solarmon/RGBtoHDMI-CDTV-v2/RGBtoHDMI CDTV v2/RGBtoHDMI CDTV v2 - Daughter Board - Top.png

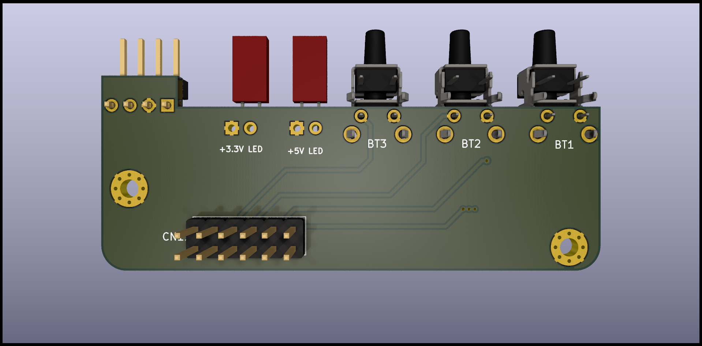
RGBtoHDMI CDTV v2/RGBtoHDMI CDTV v2 - Daughter Board - Top.png
