solarmon/RGBtoHDMI-CDTV-v2/RGBtoHDMI CDTV v2/gerbers/video-slot/RGBtoHDMI CDTV v2-Edge_Cuts.dxf

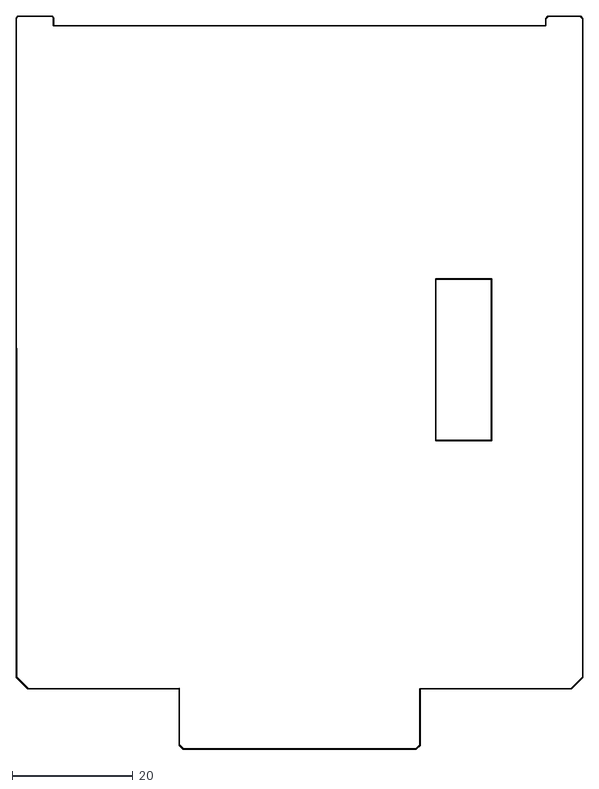
[picture p29: CAD file, 2022-10-09]
RGBtoHDMI CDTV v2/gerbers/video-slot/RGBtoHDMI CDTV v2-Edge_Cuts.dxf
94.0 x 121.6
