solarmon/RGBtoHDMI-CDTV-v2/RGBtoHDMI CDTV v2/RGBtoHDMI CDTV v2 - Face Plate.step

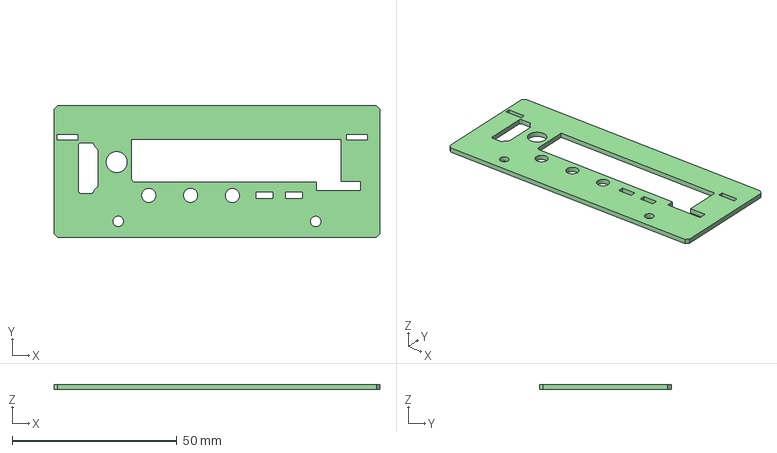
[picture p30: CAD file, 2022-10-09]
RGBtoHDMI CDTV v2/RGBtoHDMI CDTV v2 - Face Plate.step
99.0 x 40.0 x 1.60 mm
