solarmon/RGBtoHDMI-CDTV-v2/RGBtoHDMI CDTV v2 - Denise Breakout/gerber/RGBtoHDMI CDTV v2 - Denise Breakout-F_Cu.dxf

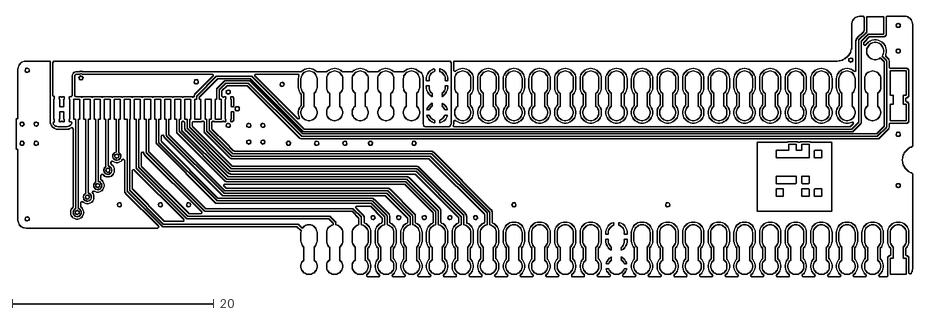
[picture p31: CAD file, 2022-10-09]
RGBtoHDMI CDTV v2 - Denise Breakout/gerber/RGBtoHDMI CDTV v2 - Denise Breakout-F_Cu.dxf
88.9 x 25.8
