solarmon/RGBtoHDMI-CDTV-v2/RGBtoHDMI CDTV v2 - Mouse and Joystick Adapter/gerber/ffc-extender/RGBtoHDMI CDTV v2 - Mouse and Joystick Adapter - FFC Extender-B_Cu.dxf

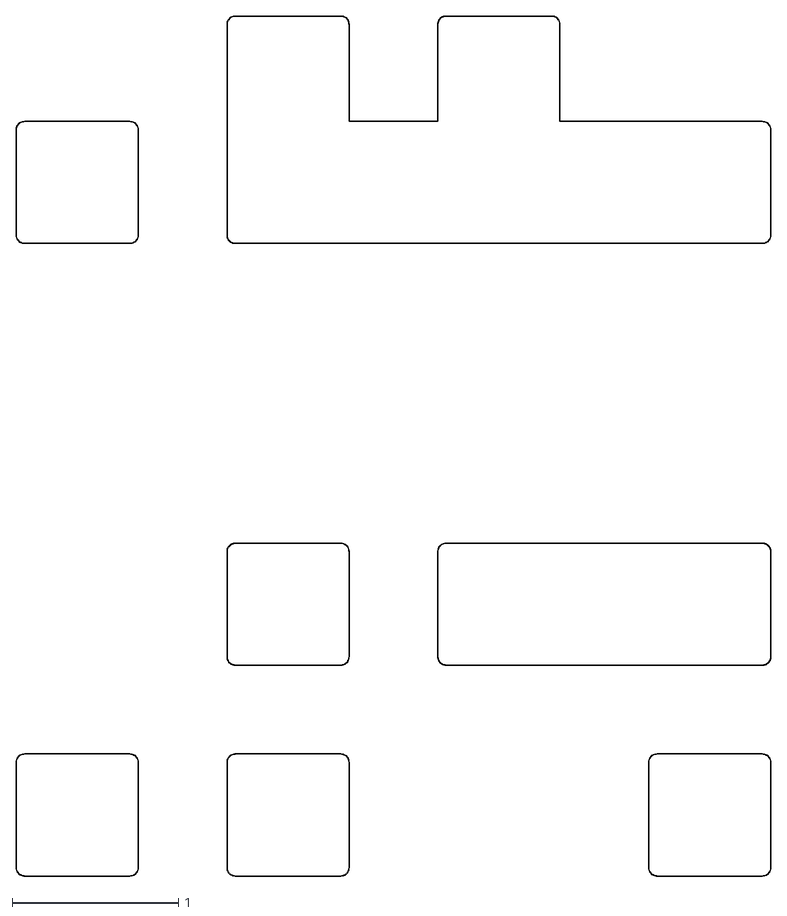
[picture p32: CAD file, 2022-10-09]
RGBtoHDMI CDTV v2 - Mouse and Joystick Adapter/gerber/ffc-extender/RGBtoHDMI CDTV v2 - Mouse and Joystick Adapter - FFC Extender-B_Cu.dxf
4.55 x 5.18
