solarmon/RGBtoHDMI-CDTV-v2/RGBtoHDMI CDTV v2 - Mouse and Joystick Adapter/gerber/mouse-joystick-adapter/RGBtoHDMI CDTV v2 - Mouse and Joystick Adapter-F_Cu.dxf

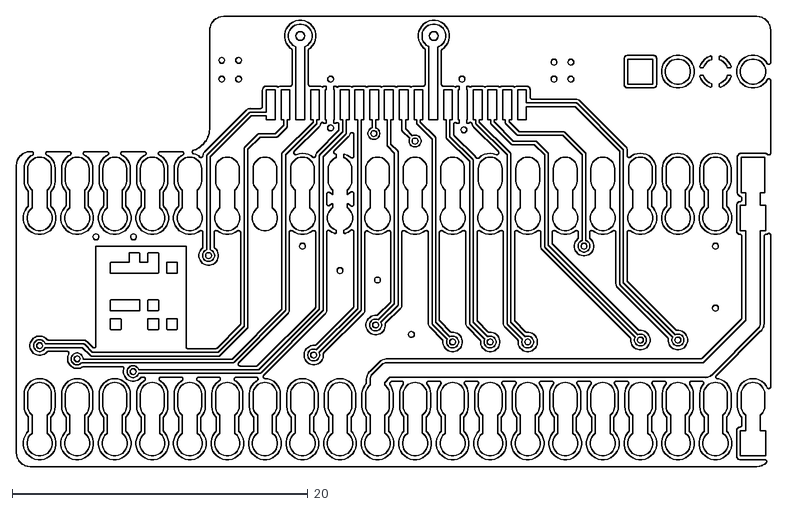
[picture p33: CAD file, 2022-10-09]
RGBtoHDMI CDTV v2 - Mouse and Joystick Adapter/gerber/mouse-joystick-adapter/RGBtoHDMI CDTV v2 - Mouse and Joystick Adapter-F_Cu.dxf
51.0 x 30.5
