solarmon/RGBtoHDMI-CDTV-v2/RGBtoHDMI CDTV v2/gerbers/daughter-board/RGBtoHDMI CDTV v2 - Daughter Board-B_Cu.dxf

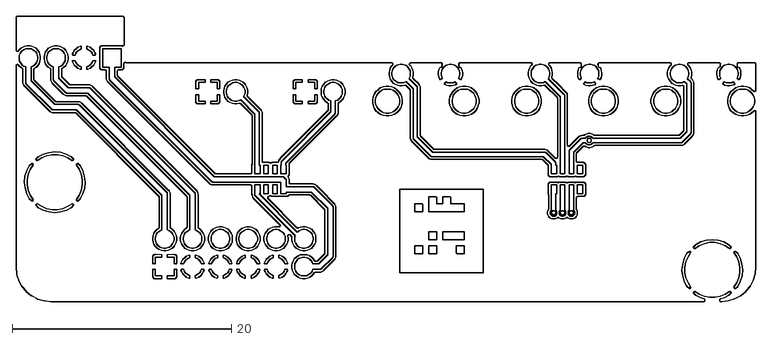
[picture p34: CAD file, 2022-10-09]
RGBtoHDMI CDTV v2/gerbers/daughter-board/RGBtoHDMI CDTV v2 - Daughter Board-B_Cu.dxf
67.5 x 26.0
