solarmon/RGBtoHDMI-CDTV-v2/RGBtoHDMI CDTV v2/gerbers/face-plate-lite/RGBtoHDMI CDTV v2 - Face Plate - Lite-Edge_Cuts.dxf

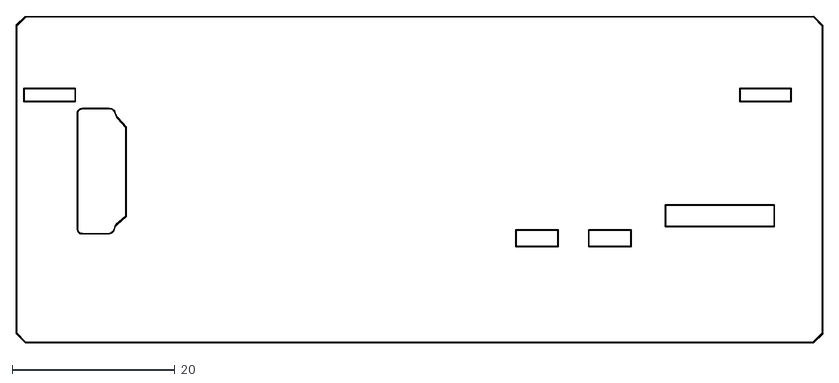
[picture p35: CAD file, 2022-10-09]
RGBtoHDMI CDTV v2/gerbers/face-plate-lite/RGBtoHDMI CDTV v2 - Face Plate - Lite-Edge_Cuts.dxf
99.0 x 40.1
