solarmon/RGBtoHDMI-CDTV-v2/RGBtoHDMI CDTV v2/gerbers/face-plate/RGBtoHDMI CDTV v2 - Face Plate-F_Cu.dxf

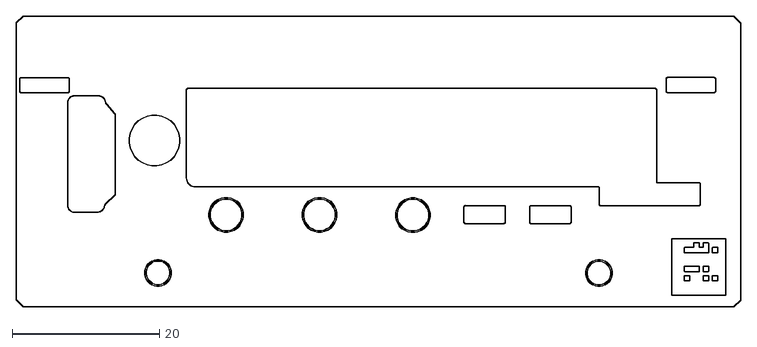
[picture p36: CAD file, 2022-10-09]
RGBtoHDMI CDTV v2/gerbers/face-plate/RGBtoHDMI CDTV v2 - Face Plate-F_Cu.dxf
98.5 x 39.6
