solarmon/RGBtoHDMI-CDTV-v2/RGBtoHDMI CDTV v2/gerbers/video-slot/RGBtoHDMI CDTV v2-F_Cu.dxf

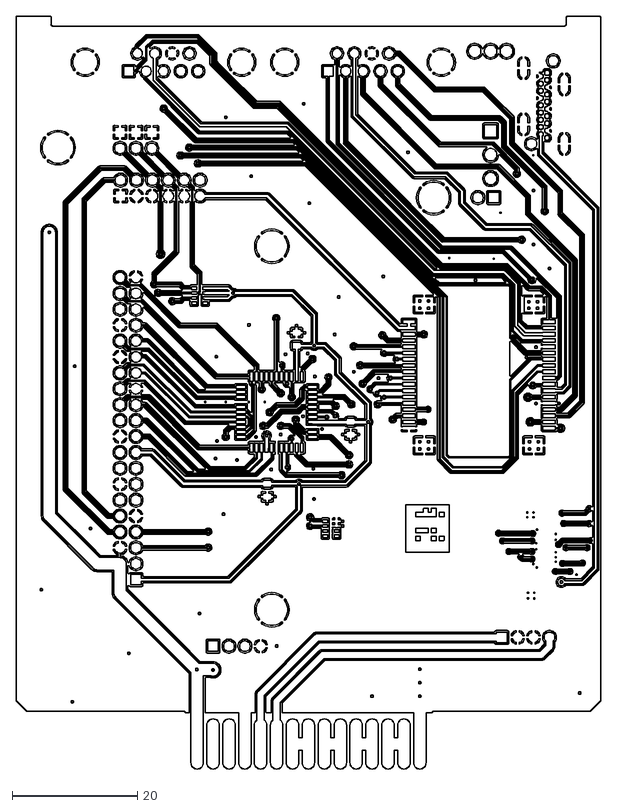
[picture p37: CAD file, 2022-10-09]
RGBtoHDMI CDTV v2/gerbers/video-slot/RGBtoHDMI CDTV v2-F_Cu.dxf
93.4 x 120.3
