solarmon/RGBtoHDMI-CDTV-v2/Installation/RGBtoHDMI CDTV v2 - Main Board - Flex Cable Warning 1.JPG

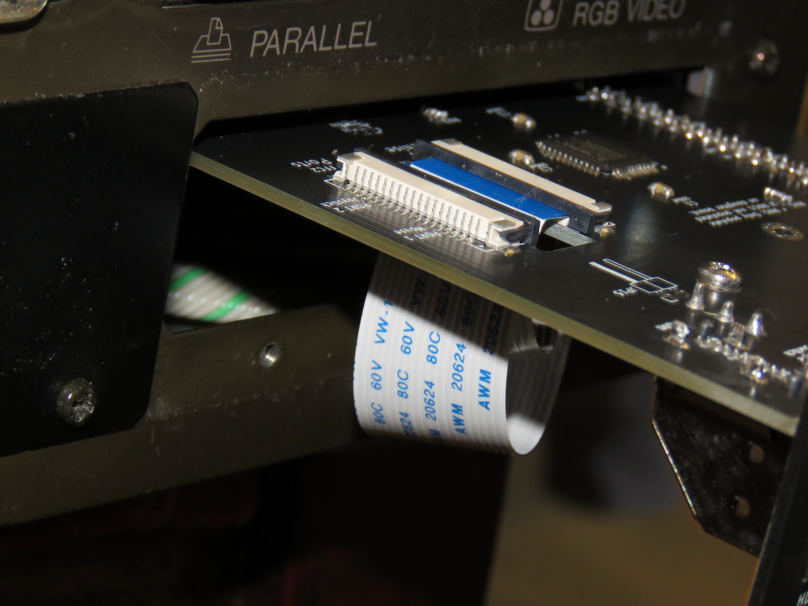
Installation/RGBtoHDMI CDTV v2 - Main Board - Flex Cable Warning 1.JPG
