solarmon/RGBtoHDMI-CDTV-v2/Installation/RGBtoHDMI CDTV v2 - Side Flex Connectors.JPG

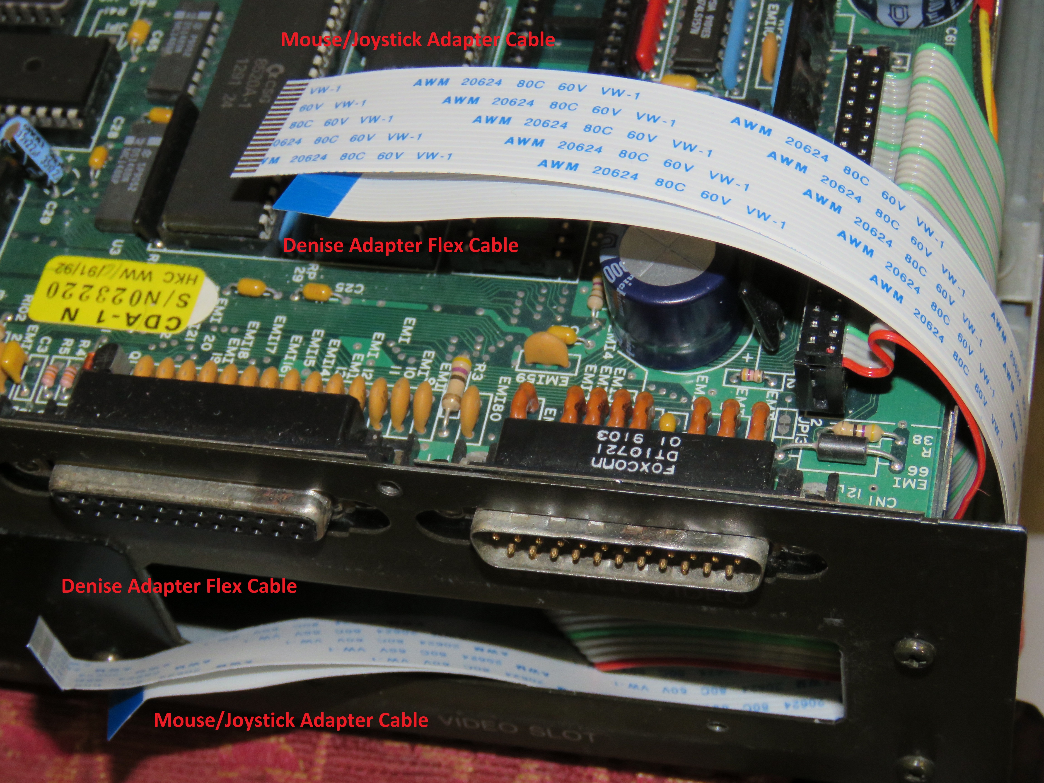
Installation/RGBtoHDMI CDTV v2 - Side Flex Connectors.JPG
