solarmon/RGBtoHDMI-CDTV-v2/Installation/RGBtoHDMI CDTV v2 - FFC Extender - Below.JPG

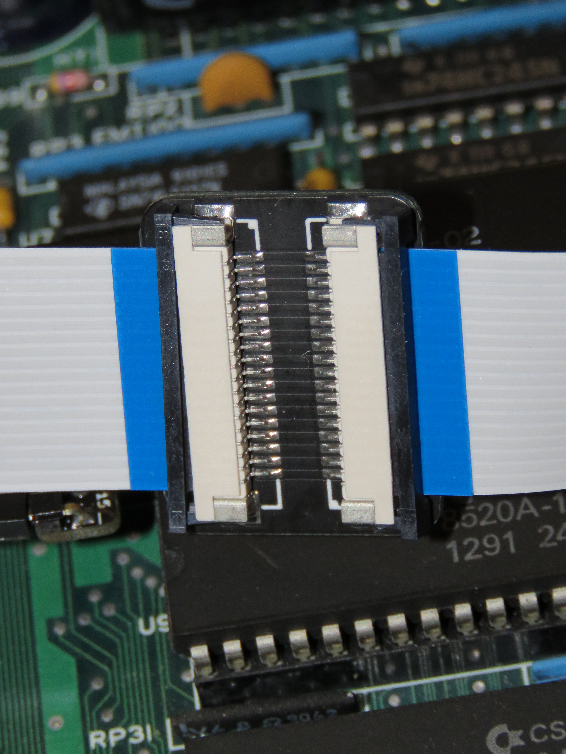
Installation/RGBtoHDMI CDTV v2 - FFC Extender - Below.JPG
